Dizzerin/Software-Defined-Radio/LTspice files/Receiver simulation.asc

C1: cap; 22n
C2: cap; 4.35n
C3: cap; 22n
C4: cap; 4.35n
C5: cap; 15p
C6: cap; 10µ
C7: cap; 15p
C8: cap; 10µ
C9: cap; 0.1µ
C10: cap; 0.1µ
C11: cap; 620p
C12: cap; 330p
C13: cap; 330p
L1: ind; 820n
L2: ind; 430n
L3: ind; 820n
R1: res; 10k
R2: res; 10k
R3: res; 10Meg
R4: res; 50
R5: res; 50
R6: res; 50
R7: res; 50
R8: res; 180
R9: res; 50k
R10: res; 180
R11: res; 50k
R12: res; 10Meg
R13: res; 10Meg
R14: res; 10Meg
R15: res; 10Meg
S1: sw; MYSW
S2: sw; MYSW
S3: sw; MYSW
S4: sw; MYSW
U1: LT6231
U2: LT6231
V1: voltage; 4.3
V2: voltage; SINE(2.15 100u {RF_freq}); AC 1; Rser=50
V7: voltage; PULSE(0 1 0 0.001p 0.001p {SW_time} {4*SW_time})
V8: voltage; PULSE(0 1 {SW_time} 0.001p 0.001p {SW_time} {4*SW_time})
V9: voltage; PULSE(0 1 {2*SW_time} 0.001p 0.001p {SW_time} {4*SW_time})
V10: voltage; PULSE(0 1 {3*SW_time} 0.001p 0.001p {SW_time} {4*SW_time})
X1: jumper
Named nets: 0, V_0_deg, V_90_deg, V_180_deg, V_270_deg, 00, 11, 01, 10, V+, V-, I, Q, AGND
;.inc LM4562Fixed.LIB
.model MYSW SW(Vt=0.9 Vh=0 Ron=1 Roff=100G)
.tran 0 0.25m 40u 5m
;.ac dec 10 10 1000Meg;
;.noise V(V_outQ) V3 dec 10 10 100meg
;.op
.param RF_freq=15Meg LO_freq={RF_freq - Audio_freq} LO_period={1/LO_freq} SW_time={LO_period/4}
Signals for voltage-controlled switches 
used to simulate our multiplexer.
Multiplexer
Simulation Control
;step oct param Audio_freq 1000 10000 1
.param Audio_freq 15000
RF signal in
BandPass Filter
Amplifiers
