Dizzerin/Software-Defined-Radio/LTspice files/MF_LPF.asc

C1: cap; 18pF
C2: cap; 0.018µF
C3: cap; 20nF
R1: res; 27k
R2: res; 50
R3: res; 330
R4: res; 50
U1: LT6231
V3: voltage; SINE(0 2 1000); AC -2 0; Rser=50
V4: voltage; ""; AC 2 0; Rser=50
V+: voltage; 5
V-: voltage; 5
Named nets: +5V, -5V, 0
.ac dec 30 1 10MEG
