Dizzerin/Software-Defined-Radio/Code/si5351_test_code/si5351_quadrature_test/si5351_quadrature_test.ino

/*
 * si5351_phase.ino - Example for setting phase with Si5351Arduino library
 *
 * Copyright (C) 2015 - 2016 Jason Milldrum <milldrum@gmail.com>
 *
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
 * You should have received a copy of the GNU General Public License
 * along with this program.  If not, see <http://www.gnu.org/licenses/>.
 */

/*
 * Setting the phase of a clock requires that you manually set the PLL and
 * take the PLL frequency into account when calculation the value to place
 * in the phase register. As shown on page 10 of Silicon Labs Application
 * Note 619 (AN619), the phase register is a 7-bit register, where a bit
 * represents a phase difference of 1/4 the PLL period. Therefore, the best
 * way to get an accurate phase setting is to make the PLL an even multiple
 * of the clock frequency, depending on what phase you need.
 *
 * If you need a 90 degree phase shift (as in many RF applications), then
 * it is quite easy to determine your parameters. Pick a PLL frequency that
 * is an even multiple of your clock frequency (remember that the PLL needs
 * to be in the range of 600 to 900 MHz). Then to set a 90 degree phase shift,
 * you simply enter that multiple into the phase register. Remember when
 * setting multiple outputs to be phase-related to each other, they each need
 * to be referenced to the same PLL.
 */

#include "si5351.h"   // NOTE: Our si5351a chip has an I2C address of 0x62 instead of the default 0x60, this was changed in the header file!
#include "Wire.h"

Si5351 si5351;

void setup()
{
  // Start serial and initialize the Si5351
  Serial.begin(9600);
  Serial.println("Program Start");
  bool i2c_found = si5351.init(SI5351_CRYSTAL_LOAD_8PF, 0, 0);
  if(!i2c_found)
  {
    Serial.println("Device not found on I2C bus!");
  }
  else
  {
    Serial.println("Device found on I2C Bus!");
  }

  // We will output 14.1 MHz on CLK0 and CLK1.
  // A PLLA frequency of 705 MHz was chosen to give an even
  // divisor by 14.1 MHz.
  unsigned long long freq = 1410000000ULL;
  unsigned long long pll_freq = 70500000000ULL;

  // Set CLK0 and CLK1 to use PLLA as the MS source.
  // This is not explicitly necessary in v2 of this library,
  // as these are already the default assignments.
  // si5351.set_ms_source(SI5351_CLK0, SI5351_PLLA);
  // si5351.set_ms_source(SI5351_CLK1, SI5351_PLLA);

  // Set CLK0 and CLK1 to output 14.1 MHz with a fixed PLL frequency
  si5351.set_freq_manual(freq, pll_freq, SI5351_CLK0);
  si5351.set_freq_manual(freq, pll_freq, SI5351_CLK1);

  // Now we can set CLK1 to have a 90 deg phase shift by entering
  // 50 in the CLK1 phase register, since the ratio of the PLL to
  // the clock frequency is 50.
  si5351.set_phase(SI5351_CLK0, 0);
  si5351.set_phase(SI5351_CLK1, 50);

  // We need to reset the PLL before they will be in phase alignment
  si5351.pll_reset(SI5351_PLLA);

  // Query a status update and wait a bit to let the Si5351 populate the
  // status flags correctly.
  si5351.update_status();
  delay(500);
}

void loop()
{
}
